dobrishinov/PowerLinkESP/Documents/All-Images/Device/6-Nicepower-Kuai-SPS-W3010.jpg

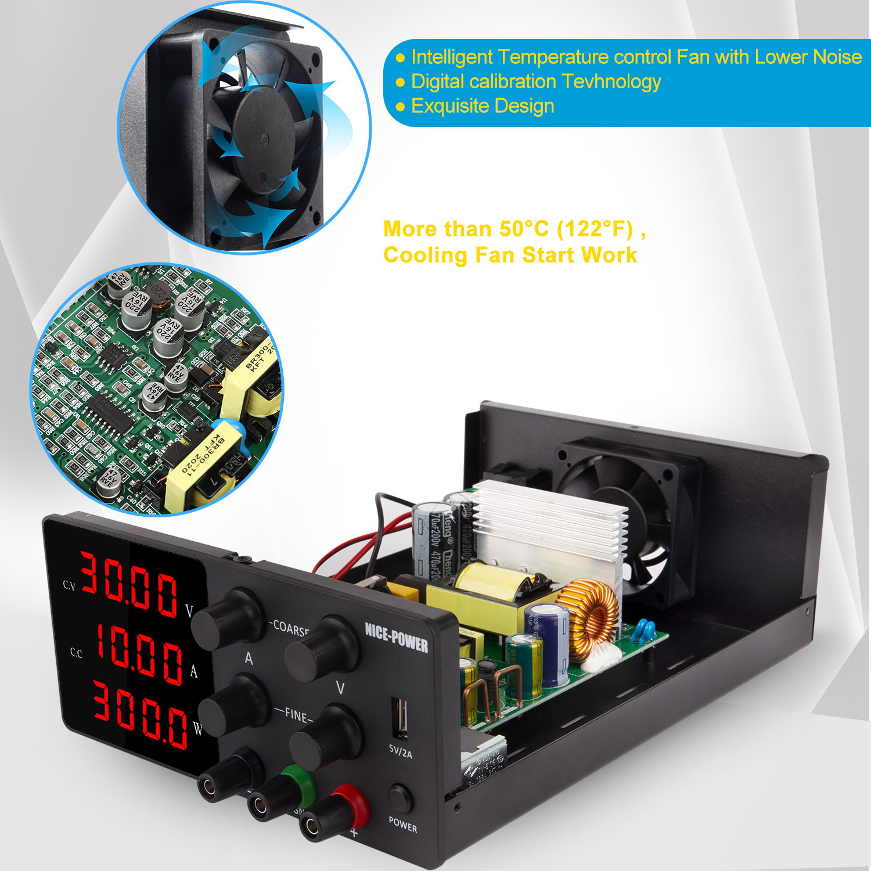
Documents/All-Images/Device/6-Nicepower-Kuai-SPS-W3010.jpg
